danielkm-ee/lora_daq_module/firmware/src/radio_board_if.c

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

/* Includes ------------------------------------------------------------------*/
#include "radio_board_if.h"

/* External variables
 * ---------------------------------------------------------*/
/* Exported functions --------------------------------------------------------*/
int32_t RBI_Init(void) {
#if defined(USE_BSP_DRIVER)
  /* Important note: BSP code is board dependent
   * STM32WL_Nucleo code can be found
   *       either in STM32CubeWL package under Drivers/BSP/STM32WLxx_Nucleo/
   *       or at
   * https://github.com/STMicroelectronics/STM32CubeWL/tree/main/Drivers/BSP/STM32WLxx_Nucleo/
   * 1/ For User boards, the BSP/STM32WLxx_Nucleo/ directory can be copied and
   * replaced in the project. The copy must then be updated depending: on board
   * RF switch configuration (pin control, number of port etc) on TCXO
   * configuration on DC/DC configuration */
  return BSP_RADIO_Init();
#else
  /* 2/ Or implement RBI_Init here */
  int32_t retcode = 0;
  /* USER CODE BEGIN RBI_Init_2 */
#warning user to provide its board code or to call his board driver functions
  /* USER CODE END RBI_Init_2 */
  return retcode;
#endif /* USE_BSP_DRIVER  */
}

int32_t RBI_DeInit(void) {
#if defined(USE_BSP_DRIVER)
  /* Important note: BSP code is board dependent
   * STM32WL_Nucleo code can be found
   *       either in STM32CubeWL package under Drivers/BSP/STM32WLxx_Nucleo/
   *       or at
   * https://github.com/STMicroelectronics/STM32CubeWL/tree/main/Drivers/BSP/STM32WLxx_Nucleo/
   * 1/ For User boards, the BSP/STM32WLxx_Nucleo/ directory can be copied and
   * replaced in the project. The copy must then be updated depending: on board
   * RF switch configuration (pin control, number of port etc) on TCXO
   * configuration on DC/DC configuration */
  return BSP_RADIO_DeInit();
#else
  /* 2/ Or implement RBI_DeInit here */
  int32_t retcode = 0;
  /* USER CODE BEGIN RBI_DeInit_2 */
#warning user to provide its board code or to call his board driver functions
  /* USER CODE END RBI_DeInit_2 */
  return retcode;
#endif /* USE_BSP_DRIVER */
}

int32_t RBI_ConfigRFSwitch(RBI_Switch_TypeDef Config) {
#if defined(USE_BSP_DRIVER)

  /* Important note: BSP code is board dependent
   * STM32WL_Nucleo code can be found
   *       either in STM32CubeWL package under Drivers/BSP/STM32WLxx_Nucleo/
   *       or at
   * https://github.com/STMicroelectronics/STM32CubeWL/tree/main/Drivers/BSP/STM32WLxx_Nucleo/
   * 1/ For User boards, the BSP/STM32WLxx_Nucleo/ directory can be copied and
   * replaced in the project. The copy must then be updated depending: on board
   * RF switch configuration (pin control, number of port etc) on TCXO
   * configuration on DC/DC configuration */
  return BSP_RADIO_ConfigRFSwitch((BSP_RADIO_Switch_TypeDef)Config);
#else
  /* 2/ Or implement RBI_ConfigRFSwitch here */
  int32_t retcode = 0;
  /* USER CODE BEGIN RBI_ConfigRFSwitch_2 */
#warning user to provide its board code or to call his board driver functions
  /* USER CODE END RBI_ConfigRFSwitch_2 */
  return retcode;
#endif /* USE_BSP_DRIVER */
}

int32_t RBI_GetTxConfig(void) {
#if defined(USE_BSP_DRIVER)
  /* Important note: BSP code is board dependent
   * STM32WL_Nucleo code can be found
   *       either in STM32CubeWL package under Drivers/BSP/STM32WLxx_Nucleo/
   *       or at
   * https://github.com/STMicroelectronics/STM32CubeWL/tree/main/Drivers/BSP/STM32WLxx_Nucleo/
   * 1/ For User boards, the BSP/STM32WLxx_Nucleo/ directory can be copied and
   * replaced in the project. The copy must then be updated depending: on board
   * RF switch configuration (pin control, number of port etc) on TCXO
   * configuration on DC/DC configuration */
  return BSP_RADIO_GetTxConfig();
#else
  /* 2/ Or implement RBI_GetTxConfig here */
  int32_t retcode = RBI_CONF_RFO;
  /* USER CODE BEGIN RBI_GetTxConfig_2 */
#warning user to provide its board code or to call his board driver functions
  /* USER CODE END RBI_GetTxConfig_2 */
  return retcode;
#endif /* USE_BSP_DRIVER */
}

int32_t RBI_IsTCXO(void) {
#if defined(USE_BSP_DRIVER)
  /* Important note: BSP code is board dependent
   * STM32WL_Nucleo code can be found
   *       either in STM32CubeWL package under Drivers/BSP/STM32WLxx_Nucleo/
   *       or at
   * https://github.com/STMicroelectronics/STM32CubeWL/tree/main/Drivers/BSP/STM32WLxx_Nucleo/
   * 1/ For User boards, the BSP/STM32WLxx_Nucleo/ directory can be copied and
   * replaced in the project. The copy must then be updated depending: on board
   * RF switch configuration (pin control, number of port etc) on TCXO
   * configuration on DC/DC configuration */
  return BSP_RADIO_IsTCXO();
#else
  /* 2/ Or implement RBI_IsTCXO here */
  int32_t retcode = IS_TCXO_SUPPORTED;
  /* USER CODE BEGIN RBI_IsTCXO_2 */
#warning user to provide its board code or to call his board driver functions
  /* USER CODE END RBI_IsTCXO_2 */
  return retcode;
#endif /* USE_BSP_DRIVER  */
}

int32_t RBI_IsDCDC(void) {
#if defined(USE_BSP_DRIVER)
  /* Important note: BSP code is board dependent
   * STM32WL_Nucleo code can be found
   *       either in STM32CubeWL package under Drivers/BSP/STM32WLxx_Nucleo/
   *       or at
   * https://github.com/STMicroelectronics/STM32CubeWL/tree/main/Drivers/BSP/STM32WLxx_Nucleo/
   * 1/ For User boards, the BSP/STM32WLxx_Nucleo/ directory can be copied and
   * replaced in the project. The copy must then be updated depending: on board
   * RF switch configuration (pin control, number of port etc) on TCXO
   * configuration on DC/DC configuration */
  return BSP_RADIO_IsDCDC();
#else
  /* 2/ Or implement RBI_IsDCDC here */
  int32_t retcode = IS_DCDC_SUPPORTED;
  /* USER CODE BEGIN RBI_IsDCDC_2 */
#warning user to provide its board code or to call his board driver functions
  /* USER CODE END RBI_IsDCDC_2 */
  return retcode;
#endif /* USE_BSP_DRIVER  */
}

/* Private Functions Definition
 * -----------------------------------------------*/
/************************ (C) COPYRIGHT STMicroelectronics *****END OF FILE****/
