danielkm-ee/lora_daq_module/firmware/src/sys_conf.h

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

/* Define to prevent recursive inclusion -------------------------------------*/
#ifndef __SYS_CONF_H__
#define __SYS_CONF_H__

#ifdef __cplusplus
extern "C" {
#endif

/* Includes ------------------------------------------------------------------*/
/* Exported types ------------------------------------------------------------*/
/* Exported constants --------------------------------------------------------*/

/**
 * @brief Temperature and pressure values are retrieved from sensors shield
 *        (instead of sending dummy values). It requires MEMS IKS shield
 */
#define SENSOR_ENABLED 0

/**
 * @brief  Verbose level for all trace logs
 */
#define VERBOSE_LEVEL VLEVEL_M

/**
 * @brief Enable trace logs
 */
#define APP_LOG_ENABLED 1

/**
 * @brief Enable MCU Debugger pins (dbg serial wires, sbg spi, etc)
 */
#define DEBUGGER_ENABLED 0

/**
 * @brief Enable four wires usable as probes (two of them PROBE1 and PROBE2 used
 * by the MW)
 */
#define PROBE_PINS_ENABLED 0

/**
 * @brief Disable Low Power mode
 * @note  0: LowPowerMode enabled. MCU enters stop2 mode, 1: LowPowerMode
 * disabled. MCU enters sleep mode only
 */
#define LOW_POWER_DISABLE 0

/* External variables --------------------------------------------------------*/
/* Exported macro ------------------------------------------------------------*/
/* Exported functions prototypes ---------------------------------------------*/
#ifdef __cplusplus
}
#endif

#endif /* __SYS_CONF_H__ */

/************************ (C) COPYRIGHT STMicroelectronics *****END OF FILE****/
